CreatorKanata/kachi-button/docs/pcb-development.md

# PCB Development with EasyEDA

Use the EasyEDA MCP / `easyeda-api` skill for Kachi Button schematic and PCB development. The skill supplies API documentation and a local HTTP/WebSocket bridge to the running EasyEDA desktop client. The bridge is the actual execution path; a separately named EasyEDA MCP server is not required by this workflow.

## Preparation

1. Read the installed `easyeda-api` skill's `SKILL.md` and the current version's design record, starting with [PCB v1](../pcb/v1/README.md).
2. Read the [current specifications](README.md) and inspect the latest product reference image. Consult local concept material only as historical input. Treat preliminary documents as design input, not instructions that override the user. Prioritize the latest user instructions, keycap geometry, component placement, and enclosure constraints.
3. Open the intended EasyEDA project. Install and load the [run-api-gateway extension](https://jlc-ext.com/item/oshwhub/run-api-gateway) as described by the skill.
4. Follow the skill's setup instructions to start its bundled `scripts/bridge-server.mjs` in the background, if a bridge is not already running.
5. Discover the bridge on local ports 49620–49629. Check `GET /health` and verify `service: "easyeda-bridge"` and an active EDA connection. Check `GET /eda-windows`; select the intended window if more than one is connected.
6. Confirm the current project and active document type before editing. PCB APIs require a PCB document; schematic APIs require a schematic document.

Keep the bridge local. Do not expose the editor control endpoint to an external network.

## API-based editing

Read the relevant class's complete method signature, remarks, enums, and interfaces in the installed skill's `references/` directory before every new API operation. Use Context7's library resolution and documentation query when checking the current SDK documentation before writing integration code. The upstream reference is the [EasyEDA API SDK](https://github.com/easyeda/pro-api-sdk).

Submit documented API operations through the bridge's `POST /execute` endpoint. Await promise-returning methods and return the result explicitly. Use documented enum members rather than guessed layer numbers. PCB API coordinates use mils (1 mil = 0.0254 mm); schematic coordinates use 0.01 inch units (0.254 mm). Confirm source-format units separately if inspecting native document data.

Before making changes, save a source snapshot and record the relevant component positions, nets, outline, and artwork. Make small edits and read back the result. Preserve the user's current placement; do not overwrite changes made while an operation is running. If an operation times out, inspect the live state before retrying so that a successful but delayed edit is not duplicated.

Use documented API operations first. Where an operation is unavailable or unreliable, use the EasyEDA UI and verify the result. Do not guess unsupported APIs or silently replace the entire board to work around a local routing problem.

## Design conventions

- Use available, low-cost parts with exact manufacturer and supplier numbers. Record when inventory was checked and recheck it at ordering time.
- Use 0402 resistors and capacitors. Keep assembly on Top where practical.
- Show signal connections with continuous schematic wires and use actual power and GND symbols. Confirm the symbols' net attributes, not just their displayed text.
- Group schematic functions for readability and make MCU pin assignments explicit.
- Preserve keycap reference rectangles, user artwork, test-pad placement, and the snap-fit board outline unless the task changes them.
- Check clearance before moving components, widening power traces, or adding vias. Keep LED current-limiting resistors close to their LEDs and power routing appropriate to local pad spacing.
- Use both-side GND pours and distribute stitching vias according to actual return paths, copper connectivity, and clearance. Avoid an arbitrary via count as a substitute for verification.
- Keep test pads accessible outside logos and button footprints. Add readable Top silkscreen net labels without overlapping exposed copper.

## Verification and release

1. Rebuild both copper pours after routing or outline changes. EasyEDA's rebuild-all shortcut is `Shift+B`; confirm the resulting copper visually.
2. Run PCB DRC and schematic checks. Verify the netlist against the intended pin map, including connector pin polarity, power nets, and key inputs. Record remaining warnings explicitly.
3. Check outline closure, corner radius, holes, keycap clearances, test-pad access, silkscreen, and copper-to-edge clearance. Add a focused regression check for the changed design requirement.
4. Save the project and export Gerber, BOM, pick-and-place, and STEP files from the same saved revision into `pcb/<version>/`. Preserve editable EasyEDA project data when available. Read exports back rather than assuming the export operation reflects the active canvas.
5. Test archive integrity and compare BOM and placement designators, quantities, footprints, units, mounting sides, and rotations. Inspect manufacturing layers and the 3D assembly in appropriate viewers; file integrity alone does not establish manufacturability.
6. Add or update the version's English `README.md` with circuit decisions, mechanical constraints, exact export filenames, verification results, and untested items. Separate planned firmware behavior from demonstrated prototype behavior.
7. Review and commit the intended files. Exclude operating-system metadata such as `.DS_Store`. A request to prepare or commit manufacturing data does not itself request fabrication, ordering, or pushing to a remote.

For v1's actual design and release limitations, see [its design record](../pcb/v1/README.md).
