CreatorKanata/kachi-button/images/key-cap/key-cap2.png

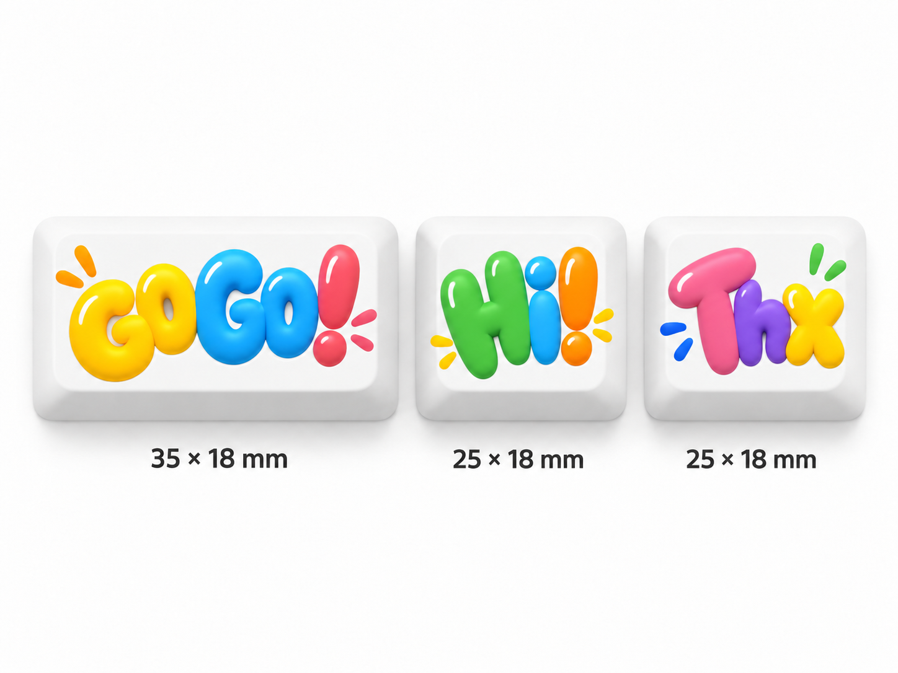
images/key-cap/key-cap2.png
