CreatorKanata/kachi-button/3d-models/key-cap/pukkuri/KachiButton-Keycap-Go-go-Raised-33x18x11.3mf

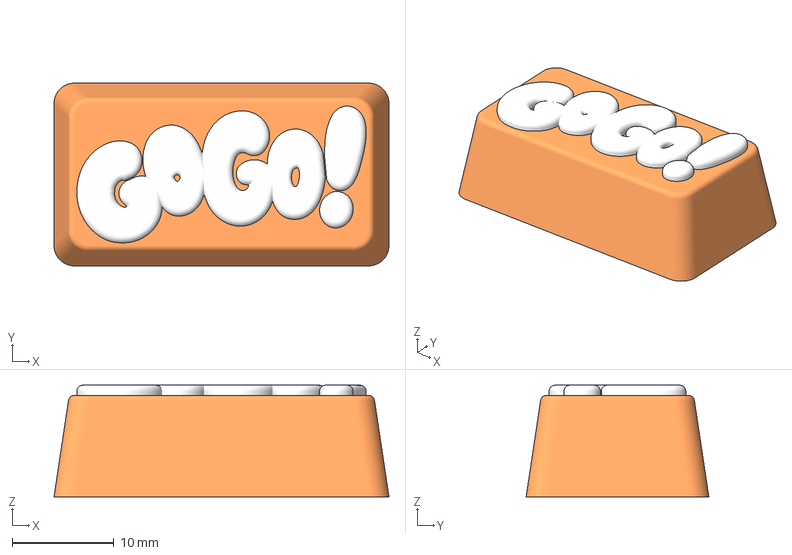
[picture p28: CAD file, 2026-09-06]
3d-models/key-cap/pukkuri/KachiButton-Keycap-Go-go-Raised-33x18x11.3mf
33.0 x 18.0 x 11.0 mm
Orange keycap shell
Raised white legend 1
Raised white legend 2
Raised white legend 3
