CreatorKanata/kachi-button/3d-models/key-cap/pukkuri2/KachiButton-Keycap-Hi-Pukkuri2-25x18x13.3mf

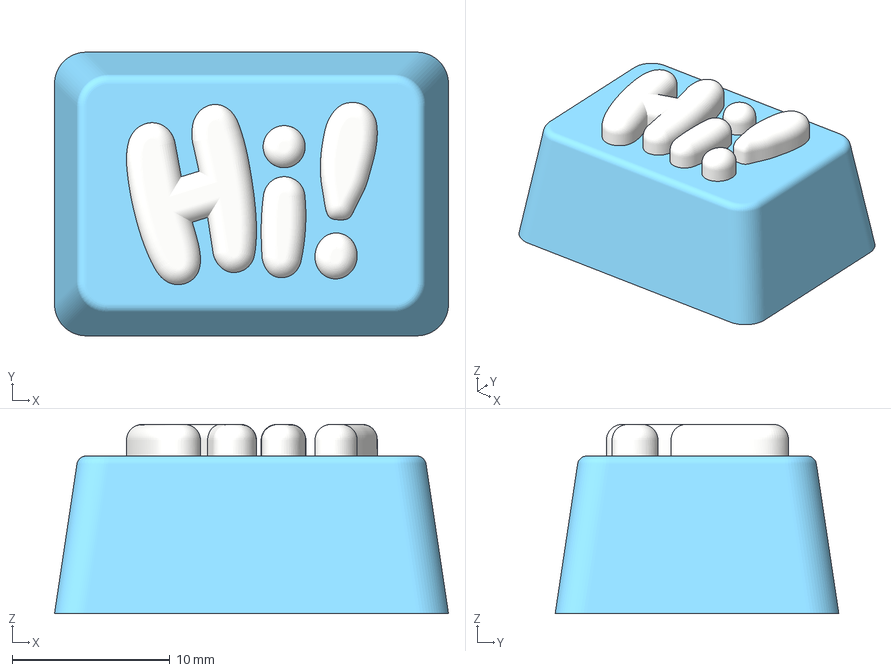
[picture p29: CAD file, 2026-09-12]
3d-models/key-cap/pukkuri2/KachiButton-Keycap-Hi-Pukkuri2-25x18x13.3mf
25.0 x 18.0 x 12.0 mm
Light blue keycap shell
Pukkuri2 Fill-11 #F77D27 H3
Pukkuri2 Fill-13 #F77D27 H3
Pukkuri2 Fill-15 #F77D27 H3
Pukkuri2 Fill-7 #2690E7 H3
Pukkuri2 Fill-9 #F77D27 H3
