CreatorKanata/kachi-button/3d-models/enclosure-pla-v1/KachiButton-Enclosure-PLA-v1-Top.stl

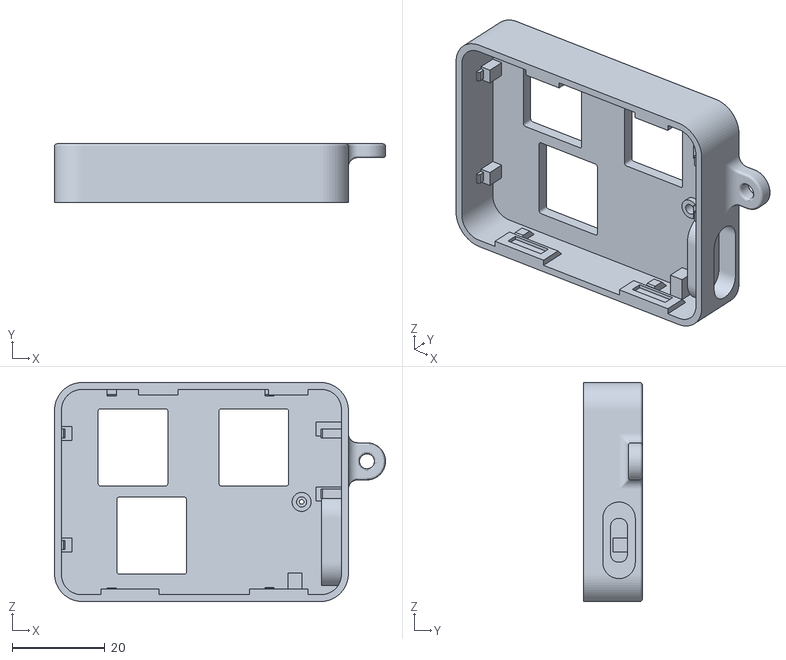
[picture p30: CAD file, 2026-09-16]
3d-models/enclosure-pla-v1/KachiButton-Enclosure-PLA-v1-Top.stl
71.3 x 12.6 x 47.2
