CreatorKanata/kachi-button/3d-models/key-cap/pukkuri2/KachiButton-Keycap-40sets-Thx-Pukkuri2.3mf

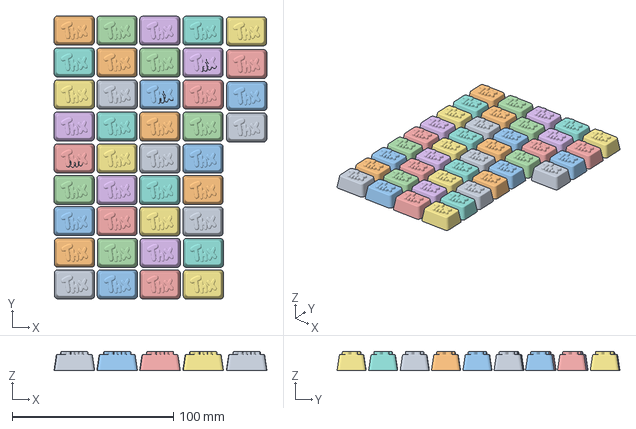
[picture p31: CAD file, 2026-09-12]
3d-models/key-cap/pukkuri2/KachiButton-Keycap-40sets-Thx-Pukkuri2.3mf
132.2 x 175.7 x 12.0 mm
KachiButton-Keycap-Thx-Pukkuri2-25x18x13 x 40
