CreatorKanata/kachi-button/images/card/makerfaire.png

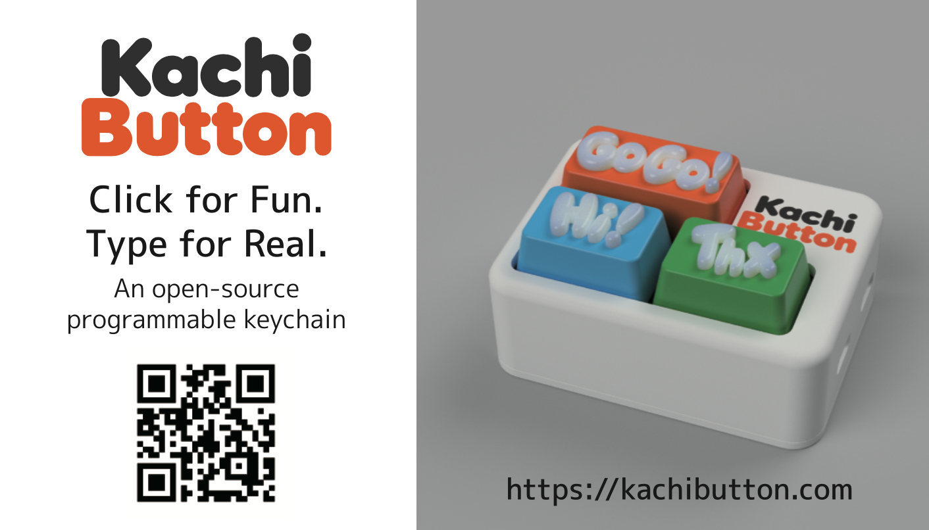
images/card/makerfaire.png
